gbotin/P2000/src/controls.h

#pragma once

#include "defines.h"

// https://github.com/JChristensen/JC_Button
#include <JC_Button.h>

bool ctrl_mode();
bool ctrl_home();
bool ctrl_move();
bool ctrl_run();
void ctrl_read();
void ctrl_setup();
bool ctrl_isDirectionUp();
bool ctrl_isDirectionDown();
Direction ctrl_getDirection();
